JGAguado/Smart_Powermeter/Design/Silkscreen/Bottom.png

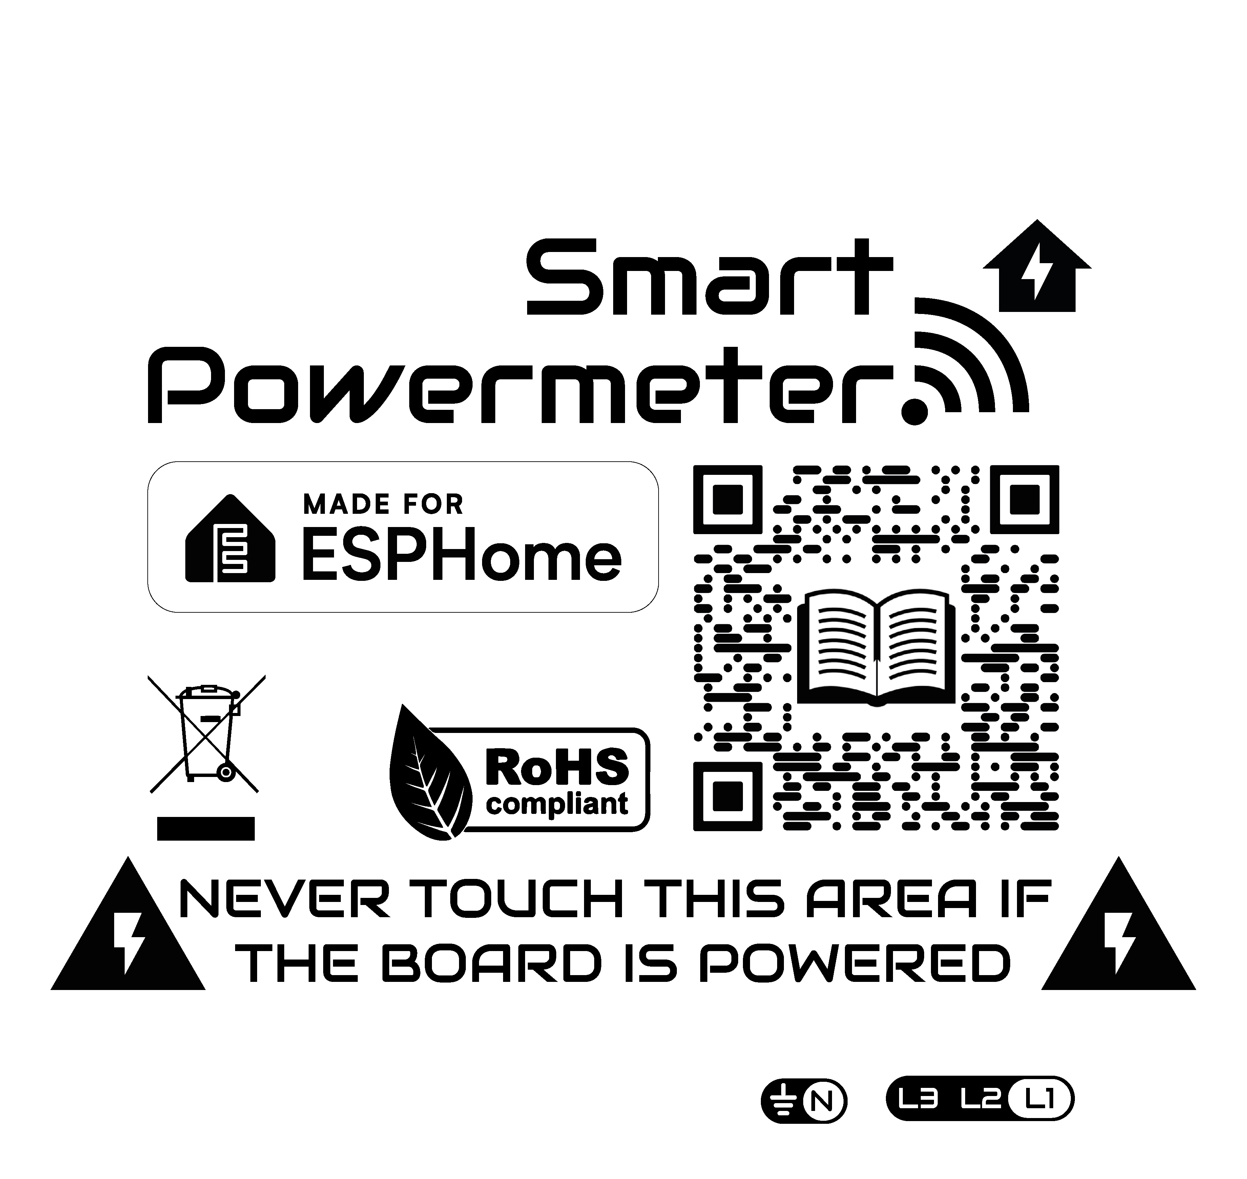
Design/Silkscreen/Bottom.png
