JGAguado/Smart_Powermeter/Design/Silkscreen/Top.png

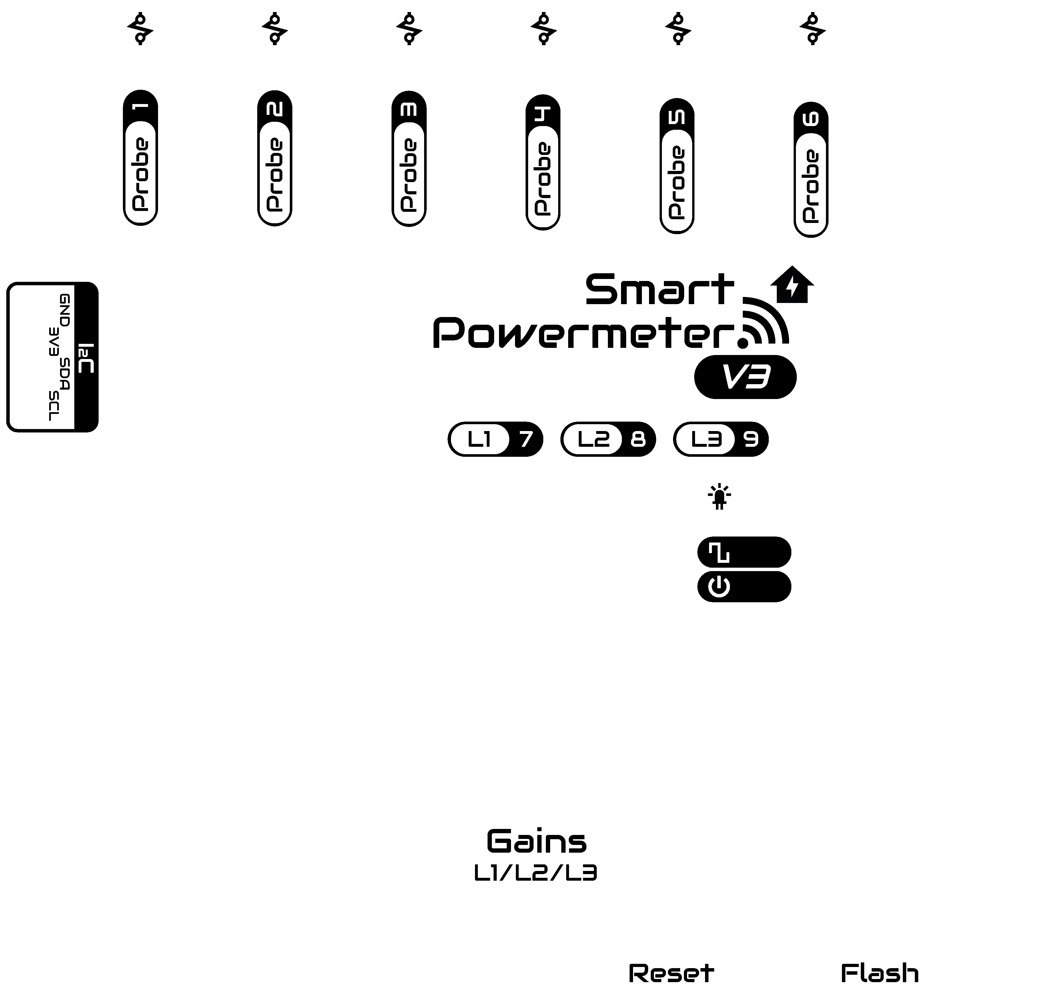
Design/Silkscreen/Top.png
