JGAguado/Smart_Powermeter/docs/source/_static/Elecrow.png

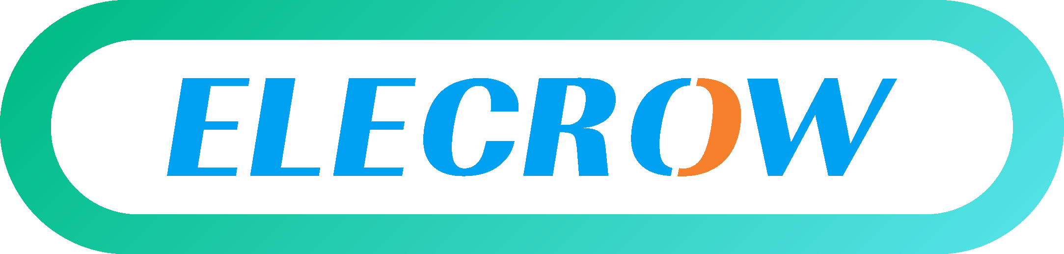
docs/source/_static/Elecrow.png
