JGAguado/Smart_Powermeter/docs/source/_static/Slide 2.png

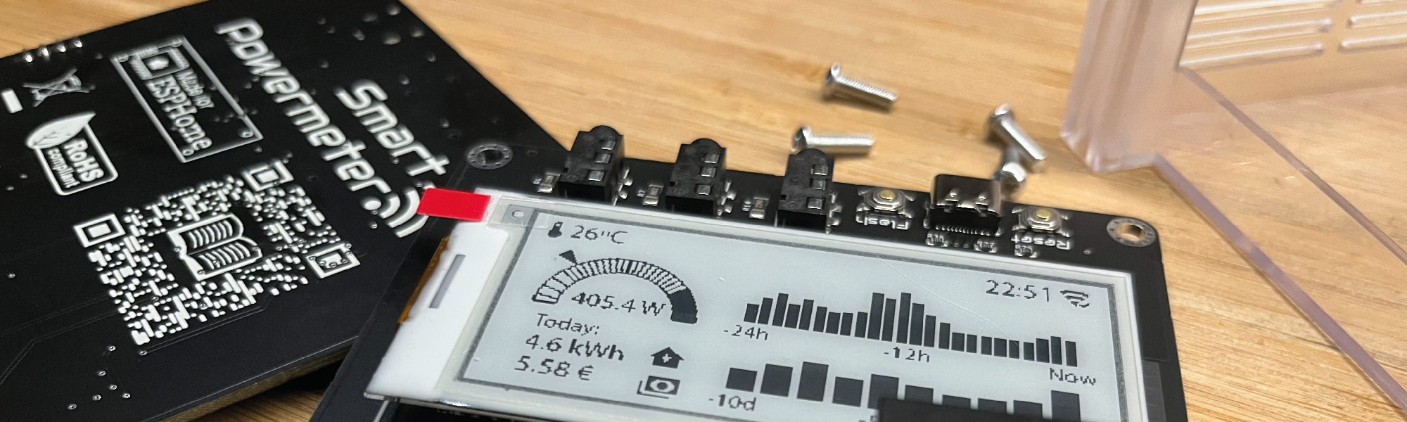
docs/source/_static/Slide 2.png
