JGAguado/Smart_Powermeter/docs/source/images/renders/Bottom.png

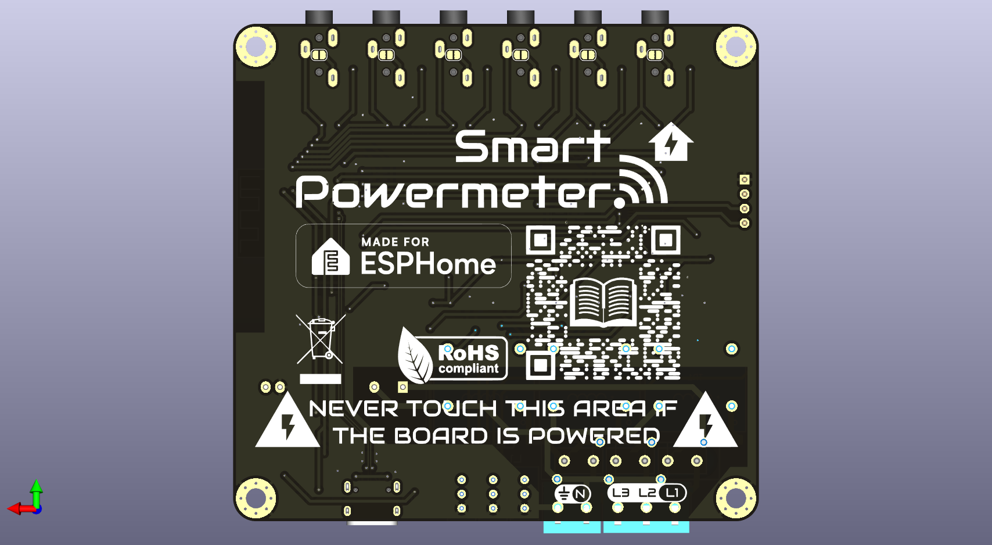
docs/source/images/renders/Bottom.png
