JGAguado/Smart_Powermeter/docs/source/images/renders/Top.png

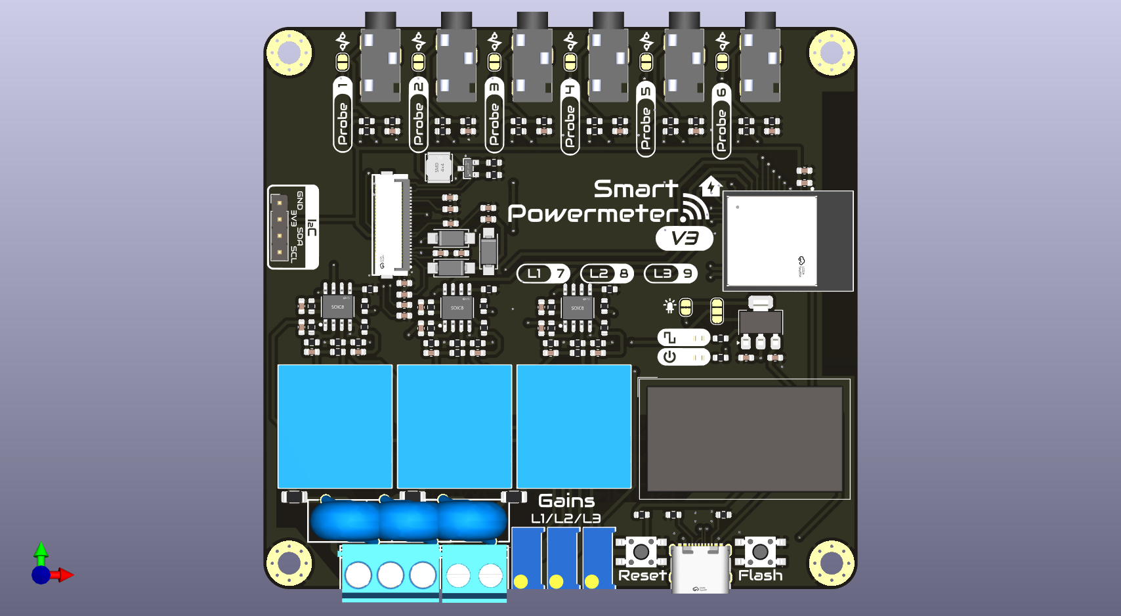
docs/source/images/renders/Top.png
