JGAguado/Smart_Powermeter/docs/source/images/assembly/TFT_display.png

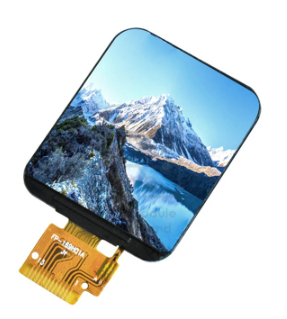
docs/source/images/assembly/TFT_display.png
